suapapa/HangulClock/rusty_hangulclock/photo/IMG_3676.jpg

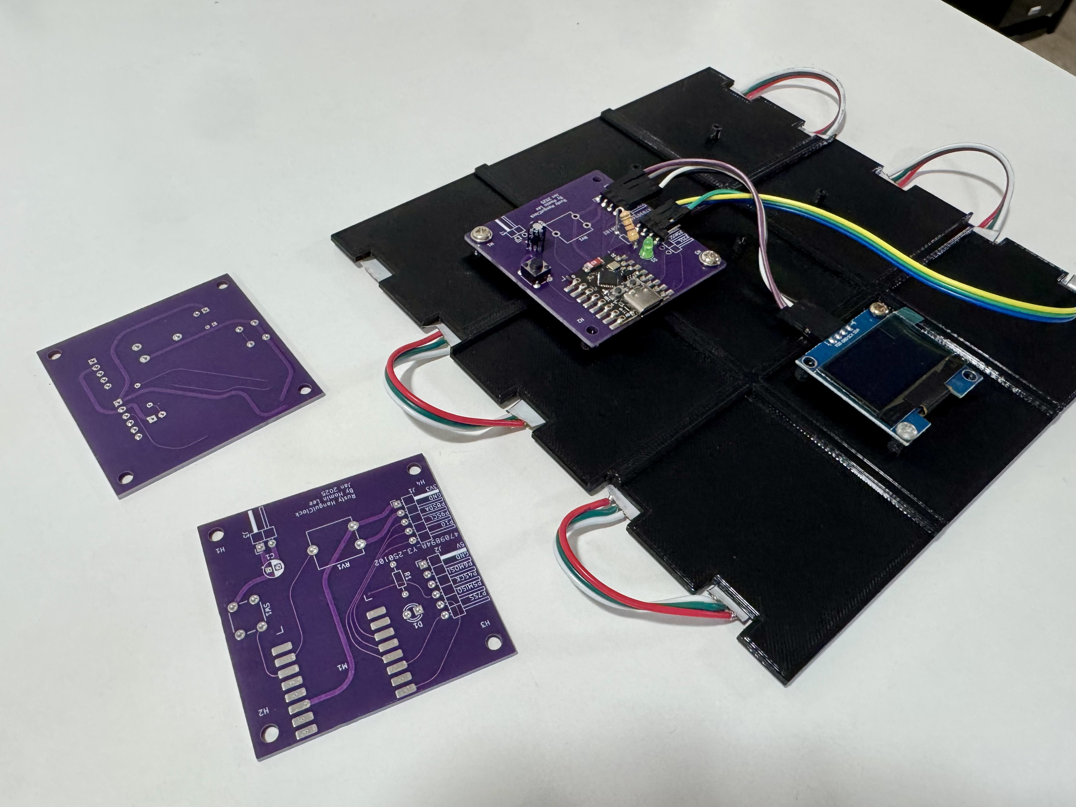
rusty_hangulclock/photo/IMG_3676.jpg
