suapapa/HangulClock/rusty_hangulclock/photo/IMG_3731.jpg

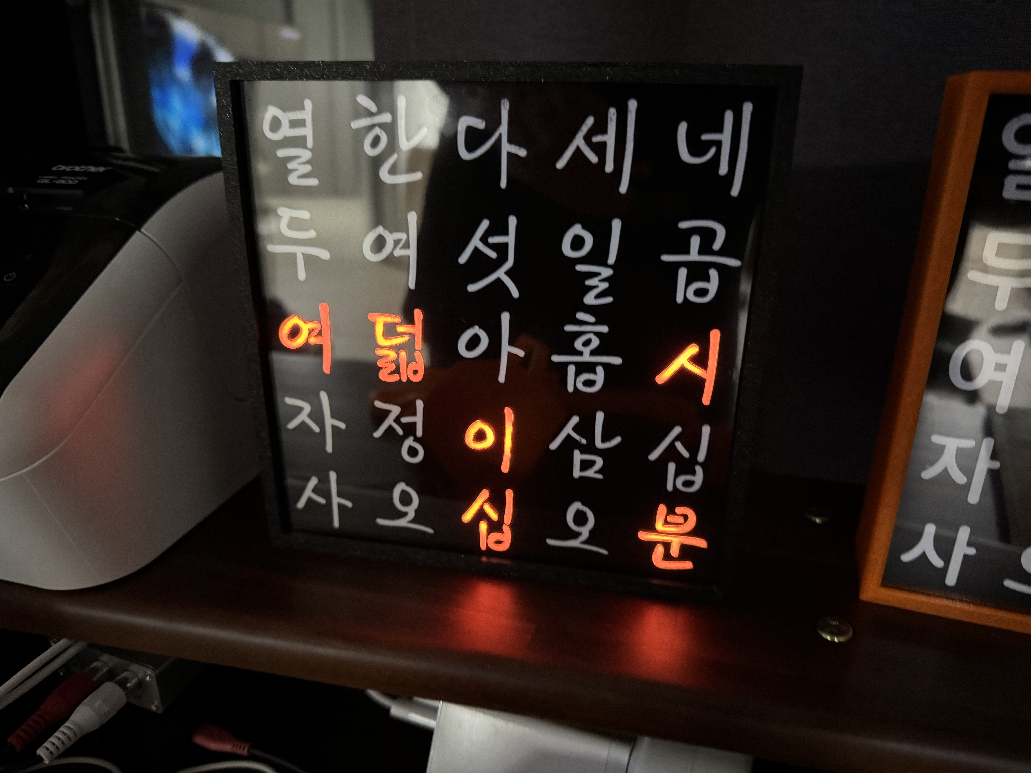
rusty_hangulclock/photo/IMG_3731.jpg
