suapapa/HangulClock/rusty_hangulclock/photo/IMG_3734.jpg

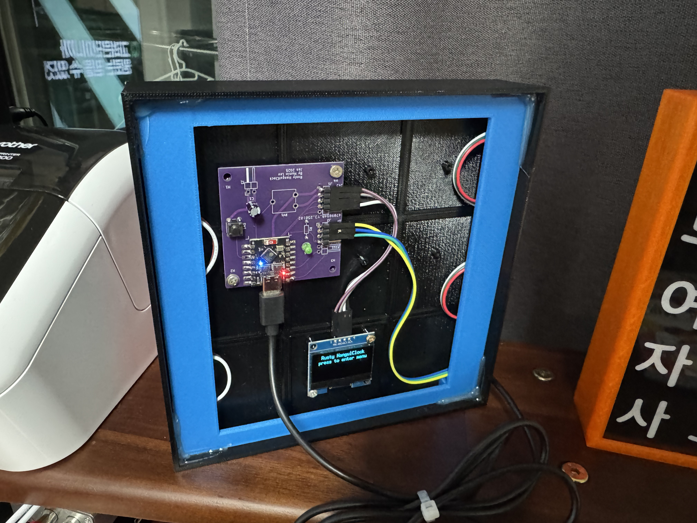
rusty_hangulclock/photo/IMG_3734.jpg
