suapapa/HangulClock/rusty_hangulclock/photo/IMG_3769.jpg

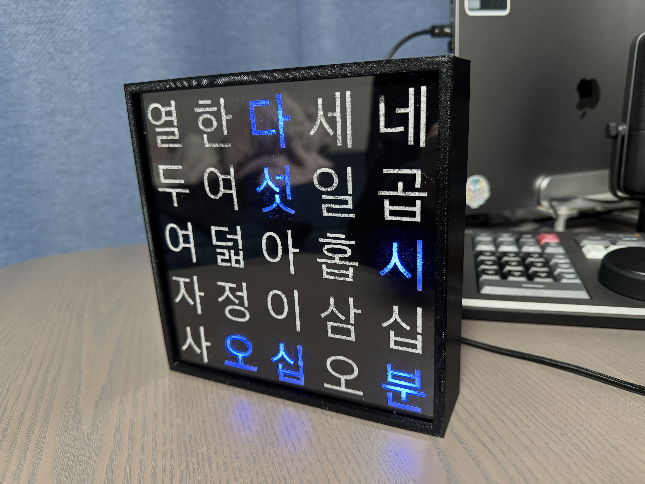
rusty_hangulclock/photo/IMG_3769.jpg
