suapapa/HangulClock/rusty_hangulclock/photo/IMG_3787.jpg

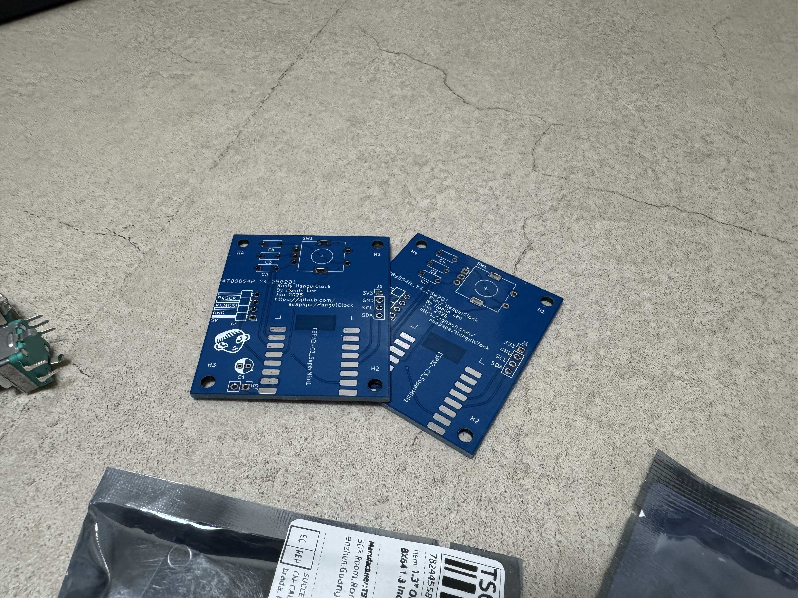
rusty_hangulclock/photo/IMG_3787.jpg
