suapapa/HangulClock/rusty_hangulclock/src/panel_apa102.rs

use apa102_spi::Apa102;
use embedded_hal;
use smart_leds::{gamma, hsv::hsv2rgb, hsv::Hsv, SmartLedsWrite, RGB8};

const LED_NUM: usize = 25;
const DEFAULT_BRIGHTNESS: u8 = 100;

pub fn welcome<SPI>(sleds: &mut Apa102<SPI>)
where
    SPI: embedded_hal::spi::SpiBus,
{
    let mut hue: u16 = 0;
    for i in 0..LED_NUM {
        let mut data = [RGB8::default(); LED_NUM];
        let color = hsv2rgb(Hsv {
            hue: hue as u8,
            sat: 255,
            val: 128, // 32,
        });
        data[i] = color;
        hue = (hue + 256 / LED_NUM as u16) % 256;
        sleds.write(gamma(data.iter().cloned())).unwrap();
        std::thread::sleep(std::time::Duration::from_millis(100));
    }

    let mut data = [RGB8::default(); LED_NUM];
    for i in 0..LED_NUM {
        let color = hsv2rgb(Hsv {
            hue: hue as u8,
            sat: 255,
            val: 128, // 32,
        });
        data[i] = color;
        hue = (hue + 256 / LED_NUM as u16) % 256;
    }
    sleds.write(gamma(data.iter().cloned())).unwrap();
}

pub fn show_time<SPI>(panel: &mut Apa102<SPI>, h: u8, m: u8)
where
    SPI: embedded_hal::spi::SpiBus,
{
    let mut h = h;
    let mut m10 = m / 10;
    let mut m1 = m % 10;
    match m1 {
        1 | 2 | 3 => m1 = 0,
        4 | 5 | 6 => m1 = 5,
        7 | 8 | 9 => {
            m1 = 0;
            m10 += 1;
            if m10 == 6 {
                m10 = 0;
                h += 1;
            }
        }
        _ => (),
    }

    if (h == 0 || h == 24) && m10 + m1 == 0 {
        show_leds(panel, vec![15, 16]); // 자정
        return;
    }

    if h == 12 && m10 + m1 == 0 {
        show_leds(panel, vec![16, 23]); // 정오
        return;
    }

    if h > 12 {
        h -= 12;
    }

    let mut leds: Vec<u8> = vec![];
    match h {
        0 | 12 => leds.extend(vec![4, 5, 10]), // 열두시
        1 => leds.extend(vec![3, 10]),         // 한시
        2 => leds.extend(vec![5, 10]),         // 두시
        3 => leds.extend(vec![1, 10]),         // 세시
        4 => leds.extend(vec![0, 10]),         // 네시
        5 => leds.extend(vec![2, 7, 10]),      // 다섯시
        6 => leds.extend(vec![6, 7, 10]),      // 여섯시
        7 => leds.extend(vec![8, 9, 10]),      // 일곱시
        8 => leds.extend(vec![14, 13, 10]),    // 여덟시
        9 => leds.extend(vec![12, 11, 10]),    // 아홉시
        10 => leds.extend(vec![4, 10]),        // 열시
        11 => leds.extend(vec![4, 3, 10]),     // 열한시
        _ => (),
    }
    if m10 + m1 != 0 {
        match m10 {
            1 => leds.extend(vec![19]),     // 십
            2 => leds.extend(vec![17, 22]), // 이십
            3 => leds.extend(vec![18, 19]), // 삼십
            4 => leds.extend(vec![24, 22]), // 사십
            5 => leds.extend(vec![23, 22]), // 오십
            _ => (),
        }
        if m1 == 5 {
            leds.extend(vec![21, 20]); // 오분
        } else {
            leds.extend(vec![20]); // 분
        }
    }
    show_leds(panel, leds);
}

fn show_leds<SPI>(panel: &mut Apa102<SPI>, leds: Vec<u8>)
where
    SPI: embedded_hal::spi::SpiBus,
{
    let mut data = [RGB8::default(); LED_NUM];
    for l in leds {
        data[l as usize] = RGB8 {
            r: 0xff, // DEFAULT_BRIGHTNESS,
            g: 0x7f, // DEFAULT_BRIGHTNESS,
            b: 0x00, // DEFAULT_BRIGHTNESS,
        };
    }

    panel.write(gamma(data.iter().cloned())).unwrap();
}
